goose35/Weather-Station/Weather_Station_V1.4/Counter.ino

//------------------------------------------------------------------------------------------------------------
/////////////////////////////////////////////// Counter /////////////////////////////////////////////////////
//------------------------------------------------------------------------------------------------------------

void Counter()
{
if (counter == UpdateInterval){

windgustmph = 0;
wind_avg = 0;
wind_min = 100;
tempc_min = 100;
tempc_max = 0;
UVmax = 0;
counter = 0;
}
counter++;

}
