goose35/Weather-Station/Weather_Station_V1.4/dewPoint.ino

//------------------------------------------------------------------------------------------------------------
///////////////////////////////////Dew point calculation//////////////////////////////////////////////////////
//------------------------------------------------------------------------------------------------------------

double dewPoint(double tempf, double humidity)
{
        double RATIO = 373.15 / (273.15 + tempf);  // RATIO was originally named A0, possibly confusing in Arduino context
        double SUM = -7.90298 * (RATIO - 1);
        SUM += 5.02808 * log10(RATIO);
        SUM += -1.3816e-7 * (pow(10, (11.344 * (1 - 1/RATIO ))) - 1) ;
        SUM += 8.1328e-3 * (pow(10, (-3.49149 * (RATIO - 1))) - 1) ;
        SUM += log10(1013.246);
        double VP = pow(10, SUM - 3) * humidity;
        double T = log(VP/0.61078);   // temp var
        return (241.88 * T) / (17.558 - T);
}

//Takes an average of readings on a given pin
//Returns the average
int averageAnalogRead(int pinToRead)
{
  byte numberOfReadings = 8;
  unsigned int runningValue = 0; 

  for(int x = 0 ; x < numberOfReadings ; x++)
    runningValue += analogRead(pinToRead);
  runningValue /= numberOfReadings;

  return(runningValue);  
}

//The Arduino Map function but for floats
//From: http://forum.arduino.cc/index.php?topic=3922.0
float mapfloat(float x, float in_min, float in_max, float out_min, float out_max)
{
  return (x - in_min) * (out_max - out_min) / (in_max - in_min) + out_min;
}
