goose35/Weather-Station/Weather_Station_V1.4/isr_rg.ino

//------------------------------------------------------------------------------------------------------------
/////////////////////////////////Rain Interrrupt handler routine//////////////////////////////////////////////
//------------------------------------------------------------------------------------------------------------
// Interrupt handler routine that is triggered when the rain sensor detects rain 
void isr_rg() {

  if((millis() - contactTime) > 15 ) { // debounce of sensor signal 
    tipCount1h++;
    tipCount24h++;
    contactTime = millis(); 
  } 
} 
