goose35/Weather-Station/Weather_Station_V1.4/isr_timer.ino

//-------------------------------------------------------------------------------------------------------------
////////////////////////////////////ISR timer//////////////////////////////////////////////////////////////////
//-------------------------------------------------------------------------------------------------------------
// isr routine for timer interrupt
void isr_timer(void){
  
  TimerCount++;
  
  if(TimerCount == 5)
  {
    IsSampleRequired = true;
    TimerCount = 0;
  }

}
