goose35/Weather-Station/Weather_Station_V1.4/setupEsp8266.ino

//------------------------------------------------------------------------------------------------------------
///////Following function setup the esp8266, put it in station made and connect to wifi access point./////////
//------------------------------------------------------------------------------------------------------------
void setupEsp8266()                                   
{
    if(DEBUG){
      Serial.println("Reseting esp8266");
    }
    esp8266Module.flush();
    esp8266Module.println(F("AT+RST"));
    delay(7000);
    if (esp8266Module.find("OK"))
    {
      if(DEBUG){
        Serial.println("Found OK");
        Serial.println("Changing espmode");
      }  
      esp8266Module.flush();
      changingMode();
      delay(5000);
      esp8266Module.flush();
      connectToWiFi();
    }
    else
    {
      if(DEBUG){
        Serial.println("OK not found");
      }
    }
}
